hcortes3109/Sensor_Goualou_Cortes/Kicad/All_composents.jpg

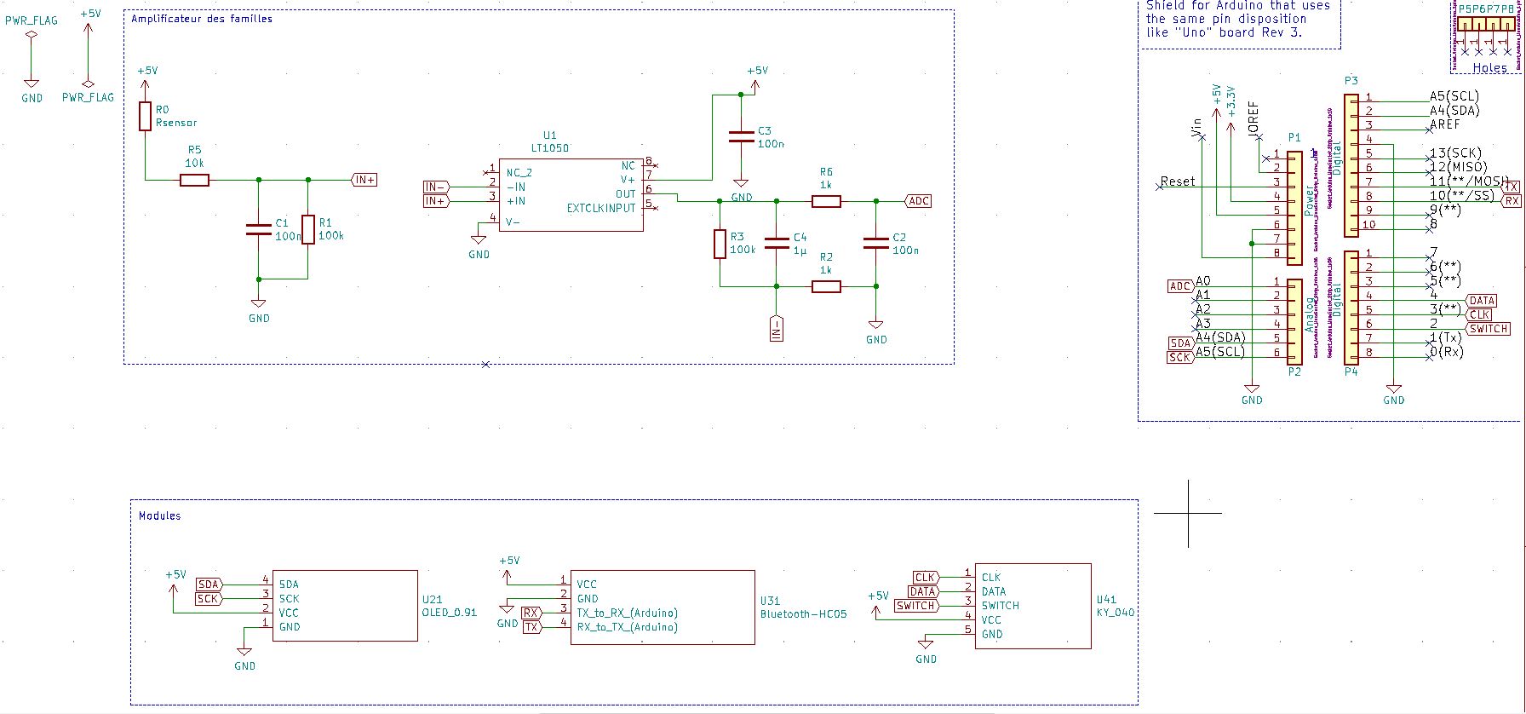
Kicad/All_composents.jpg
