hcortes3109/Sensor_Goualou_Cortes/Kicad/Ampli_transimpédance.jpg

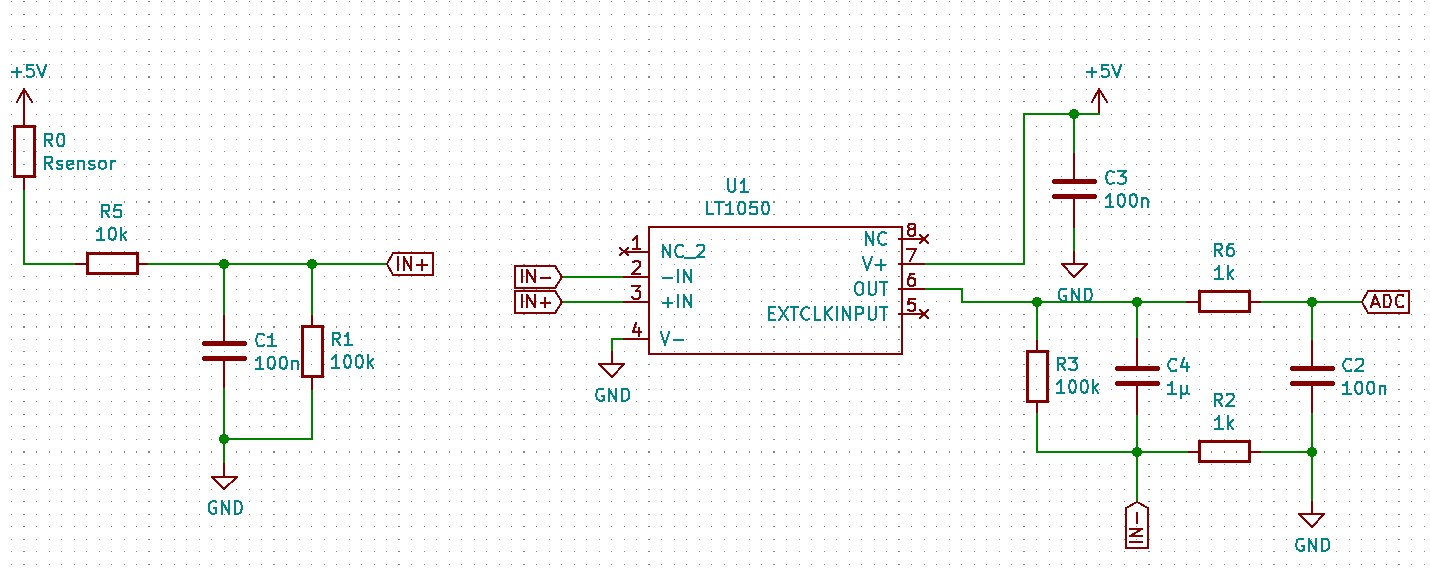
Kicad/Ampli_transimpédance.jpg
