hcortes3109/Sensor_Goualou_Cortes/Kicad/Circuit_KiCad.jpg

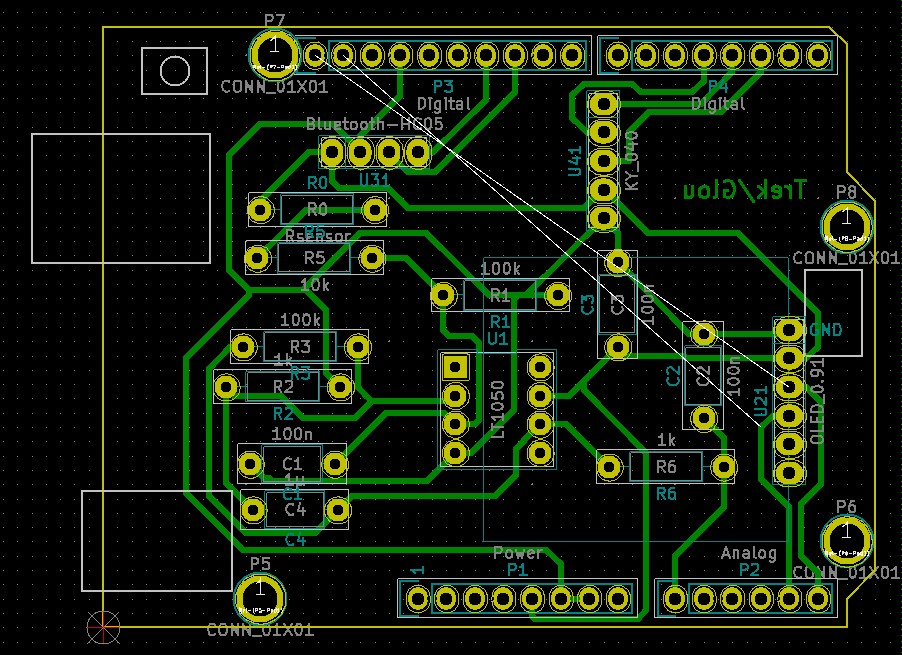
Kicad/Circuit_KiCad.jpg
