hcortes3109/Sensor_Goualou_Cortes/Kicad/Encodeur_Rotatoire.jpg

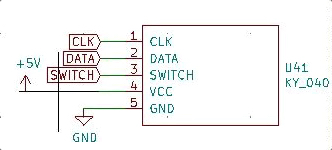
Kicad/Encodeur_Rotatoire.jpg
